loopj/short-stack/images/power-strip-render.png

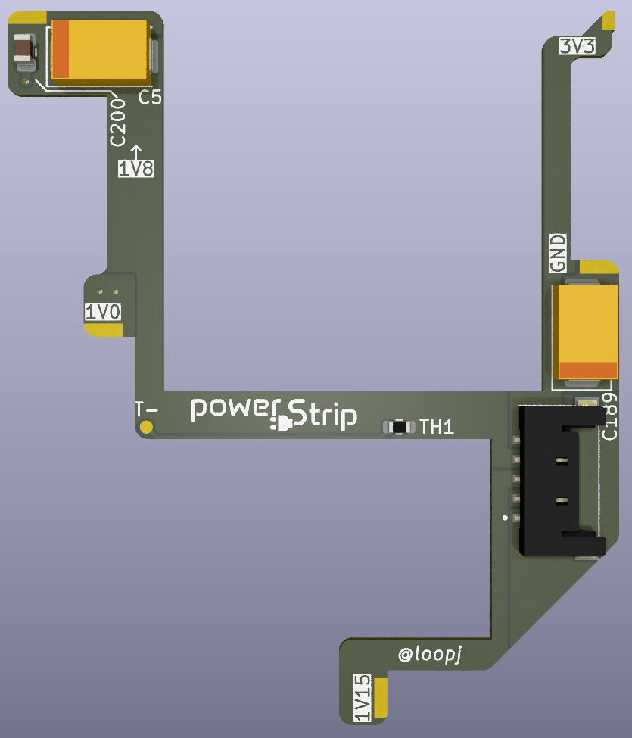
images/power-strip-render.png
