loopj/short-stack/main-board/KiCad/project-footprints/SOT-523.step

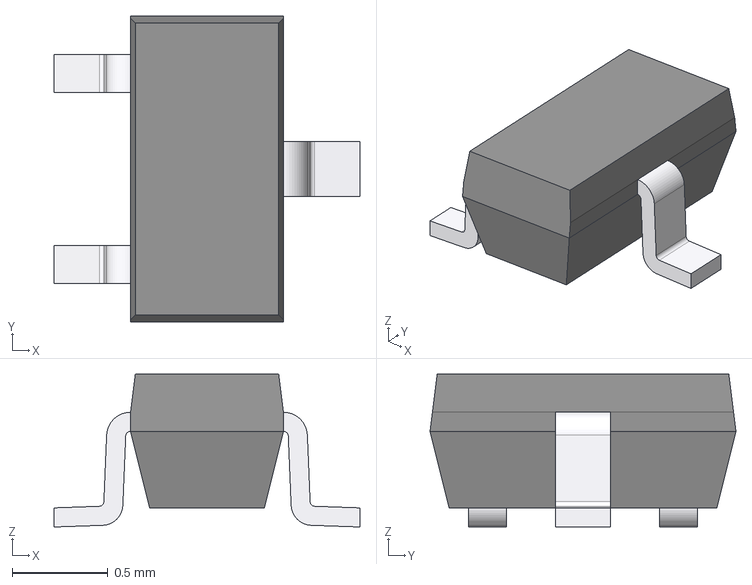
[picture p30: CAD file, 2024-04-17]
main-board/KiCad/project-footprints/SOT-523.step
1.60 x 1.60 x 0.8 mm
