loopj/short-stack/main-board/KiCad/project-footprints/IND_A220M11_VIS.step

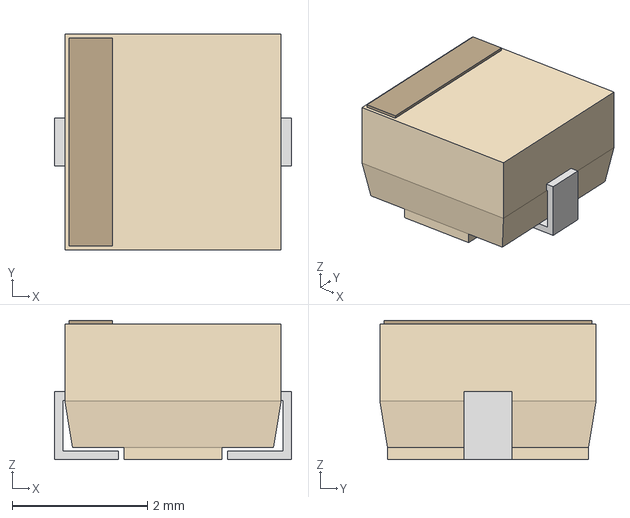
[picture p31: CAD file, 2024-04-17]
main-board/KiCad/project-footprints/IND_A220M11_VIS.step
3.51 x 3.20 x 2.06 mm
