loopj/short-stack/main-board/KiCad/project-footprints/504050-0591.stp

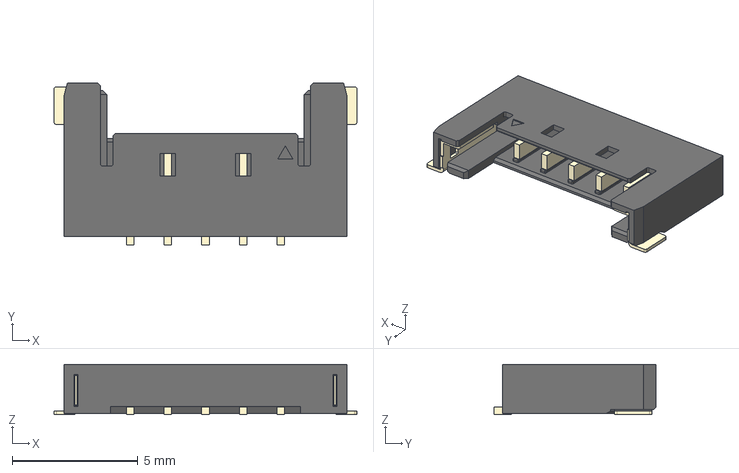
[picture p32: CAD file, 2024-04-17]
main-board/KiCad/project-footprints/504050-0591.stp
12.1 x 6.44 x 2.00 mm
