loopj/short-stack/front-panel/KiCad/project-footprints/5034800800.stp

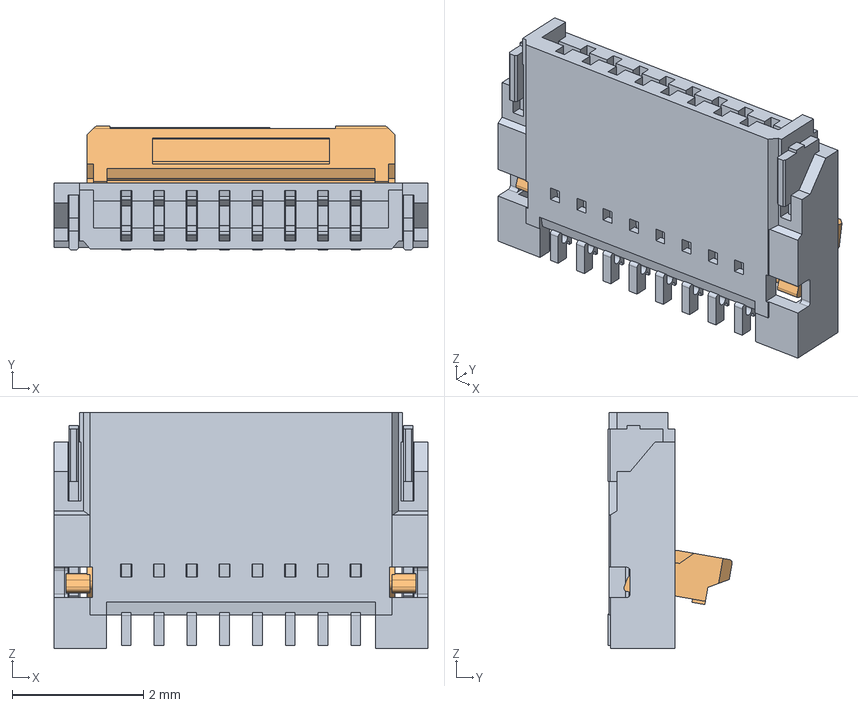
[picture p33: CAD file, 2024-04-17]
front-panel/KiCad/project-footprints/5034800800.stp
5.70 x 1.90 x 3.60 mm
